wiggle-bin/wiggle-r/Design/BinTop/TopAttachments/BreadBoardPlateLaserCut.dxf

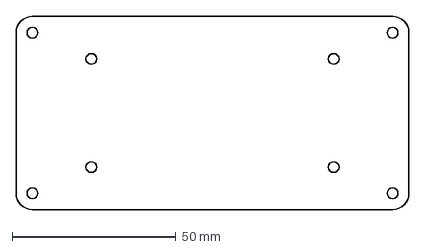
[picture p16: CAD file, 2023-12-06]
Design/BinTop/TopAttachments/BreadBoardPlateLaserCut.dxf
120.0 x 59.0 mm
