wiggle-bin/wiggle-r/Design/BinTop/TopAttachments/BreadBoardTopPlateLaserCut.dxf

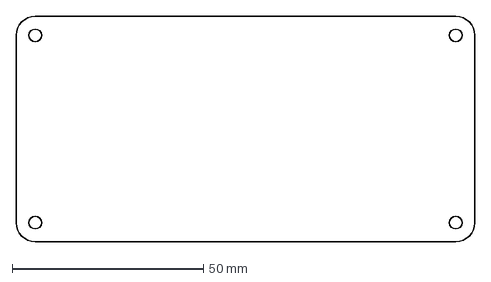
[picture p17: CAD file, 2023-12-06]
Design/BinTop/TopAttachments/BreadBoardTopPlateLaserCut.dxf
120.0 x 59.0 mm
