wiggle-bin/wiggle-r/Design/BinTop/TopAttachments/RaspberryTopPlate.dxf

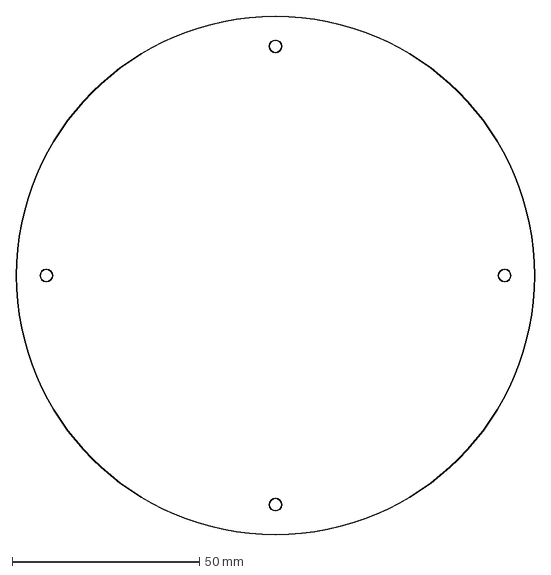
[picture p18: CAD file, 2023-12-06]
Design/BinTop/TopAttachments/RaspberryTopPlate.dxf
138.4 x 138.4 mm
